bambssquad/boq-tribun-metta/assets/r04/revit/T-01.png

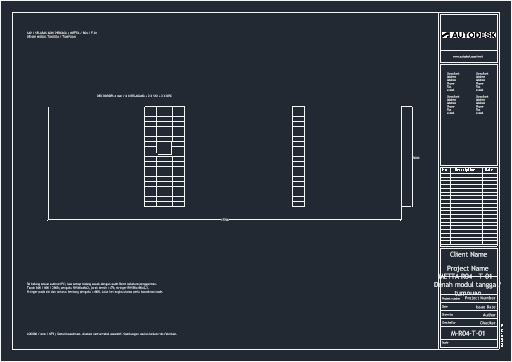
assets/r04/revit/T-01.png
