bambssquad/boq-tribun-metta/assets/r04/revit/T-03.png

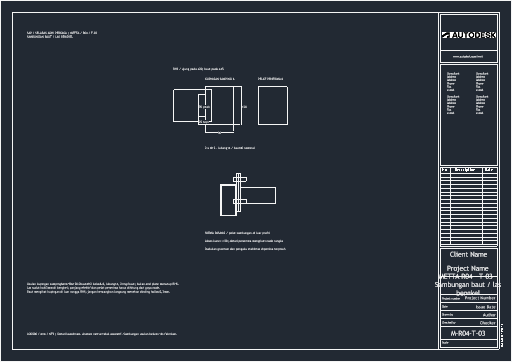
assets/r04/revit/T-03.png
