bambssquad/boq-tribun-metta/assets/r04/revit/T-04.png

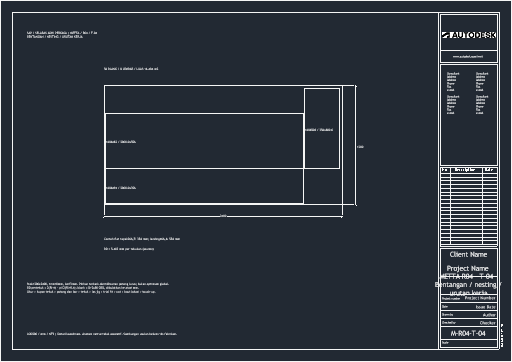
assets/r04/revit/T-04.png
