bambssquad/boq-tribun-metta/assets/technical/revit/S-02.png

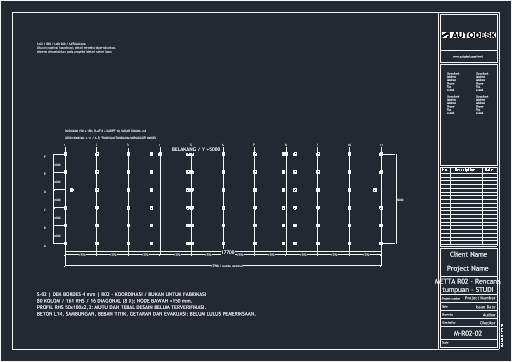
assets/technical/revit/S-02.png
