bambssquad/boq-tribun-metta/assets/technical/revit/S-03.png

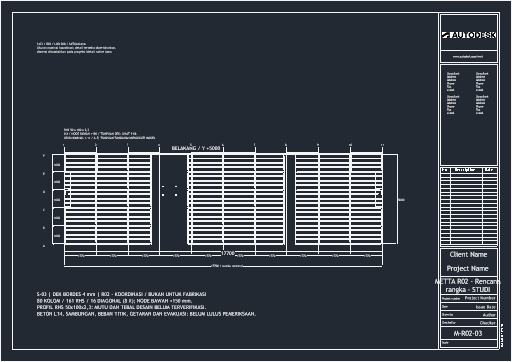
assets/technical/revit/S-03.png
