bambssquad/boq-tribun-metta/assets/technical/revit/S-04.png

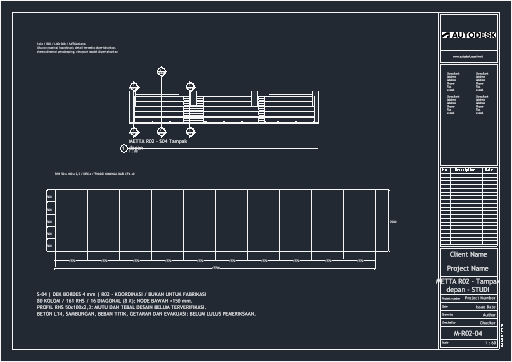
assets/technical/revit/S-04.png
