bambssquad/boq-tribun-metta/assets/technical/revit/S-06.png

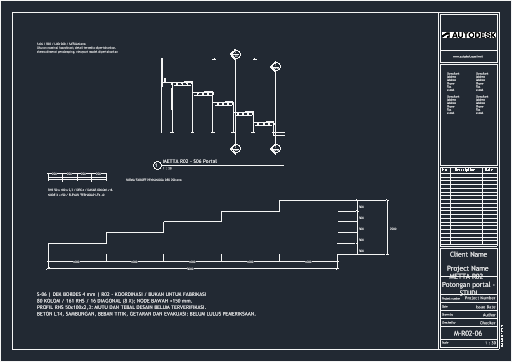
assets/technical/revit/S-06.png
