bambssquad/boq-tribun-metta/assets/technical/revit/S-07.png

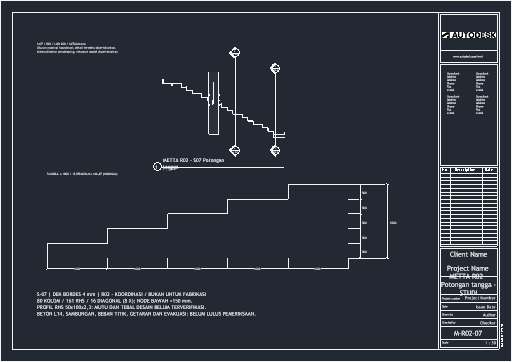
assets/technical/revit/S-07.png
