bambssquad/boq-tribun-metta/assets/technical/revit/S-08.png

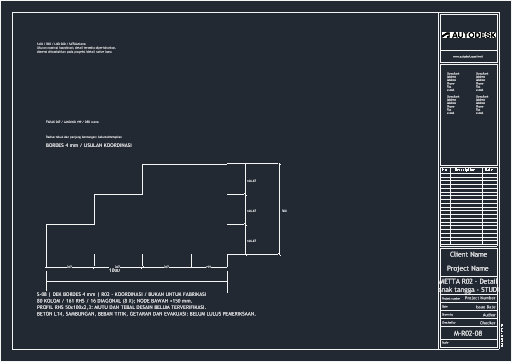
assets/technical/revit/S-08.png
