bambssquad/boq-tribun-metta/assets/technical/revit/S-09.png

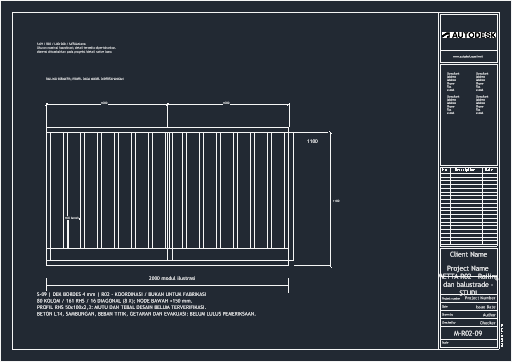
assets/technical/revit/S-09.png
