bambssquad/boq-tribun-metta/assets/technical/revit/S-10.png

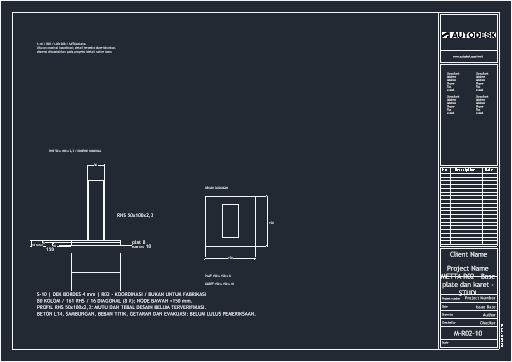
assets/technical/revit/S-10.png
