bambssquad/boq-tribun-metta/assets/technical/revit/S-12.png

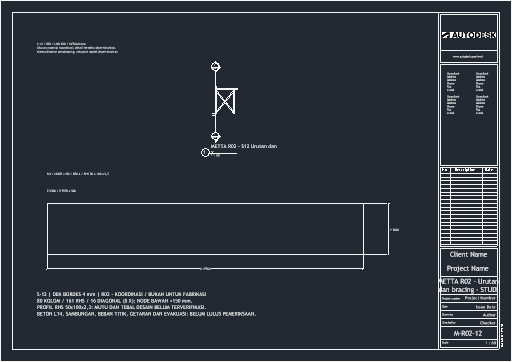
assets/technical/revit/S-12.png
