bambssquad/boq-tribun-metta/assets/technical/S-03.dxf

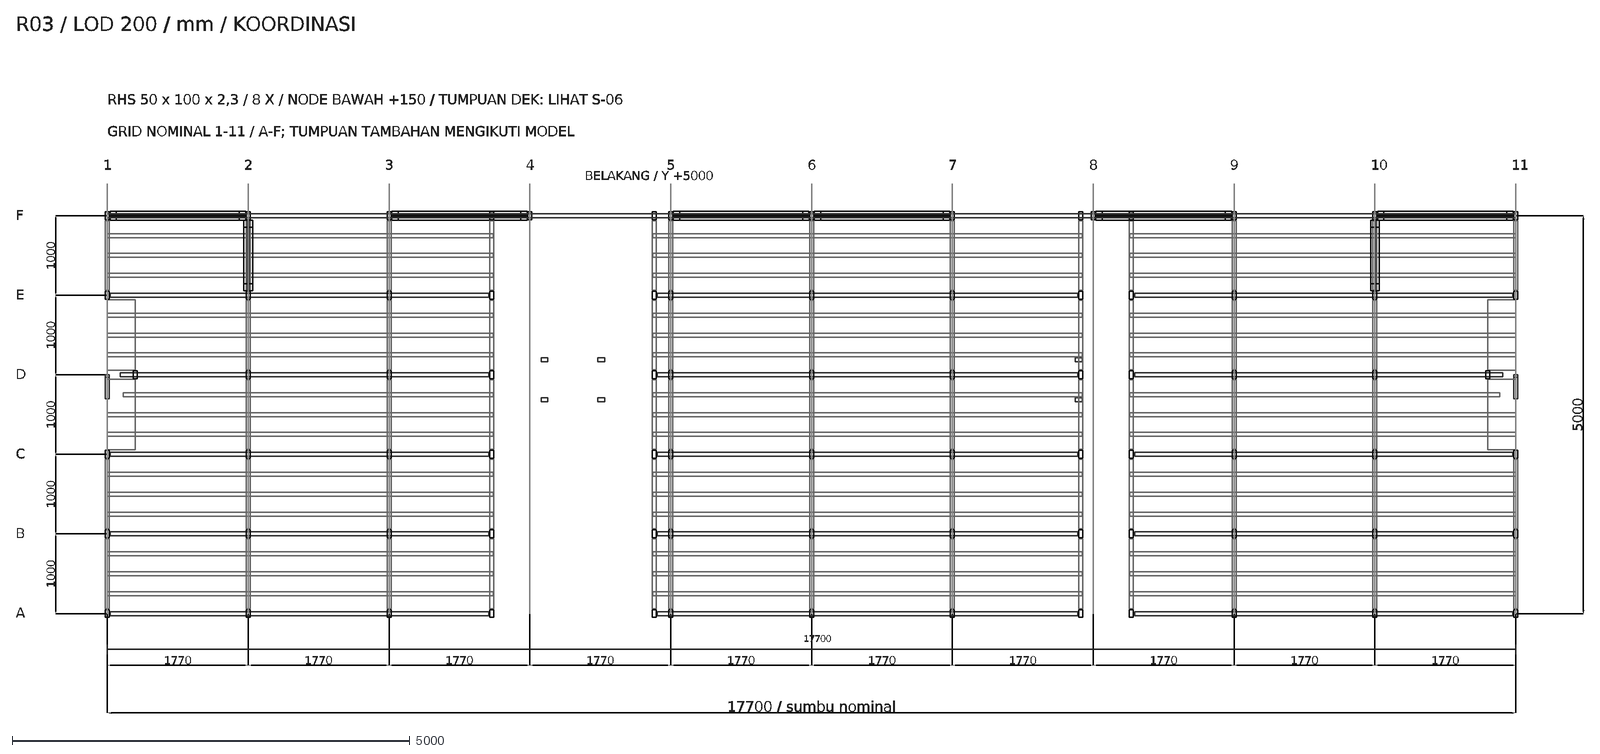
[picture p46: CAD file, 2026-09-08]
assets/technical/S-03.dxf
17700 / sumbu nominal
5000
1770
1000
17700
BELAKANG / Y +5000
1
2
3
4
5
6
7
8
9
10
11
A
B
C
D
E
F
GRID NOMINAL 1-11 / A-F; TUMPUAN TAMBAHAN MENGIKUTI MODEL
RHS 50 x 100 x 2,3 / 8 X / NODE BAWAH +150 / TUMPUAN DEK: LIHAT S-06
R03 / LOD 200 / mm / KOORDINASI
