bambssquad/boq-tribun-metta/assets/technical/S-08.dxf

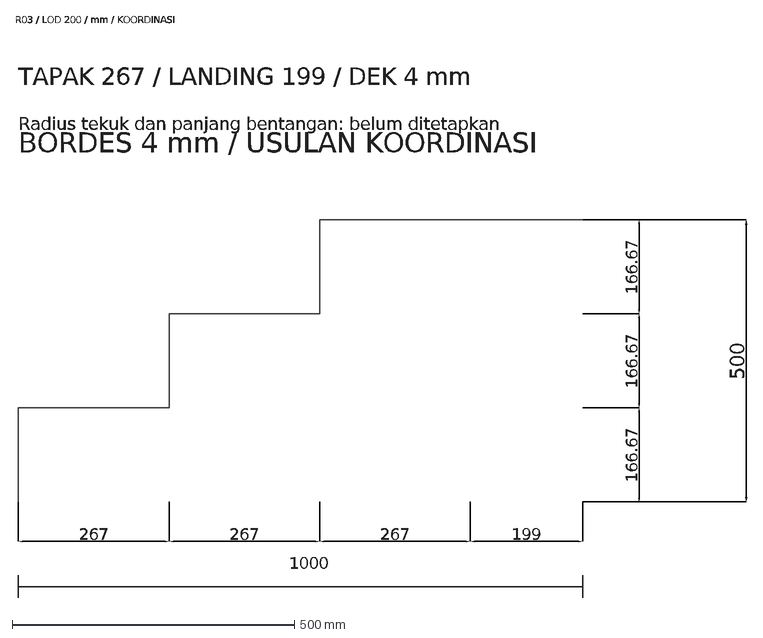
[picture p47: CAD file, 2026-09-08]
assets/technical/S-08.dxf
267
199
166.67
500
1000
BORDES 4 mm / USULAN KOORDINASI
TAPAK 267 / LANDING 199 / DEK 4 mm
Radius tekuk dan panjang bentangan: belum ditetapkan
R03 / LOD 200 / mm / KOORDINASI
