bambssquad/boq-tribun-metta/assets/technical/S-05.dxf

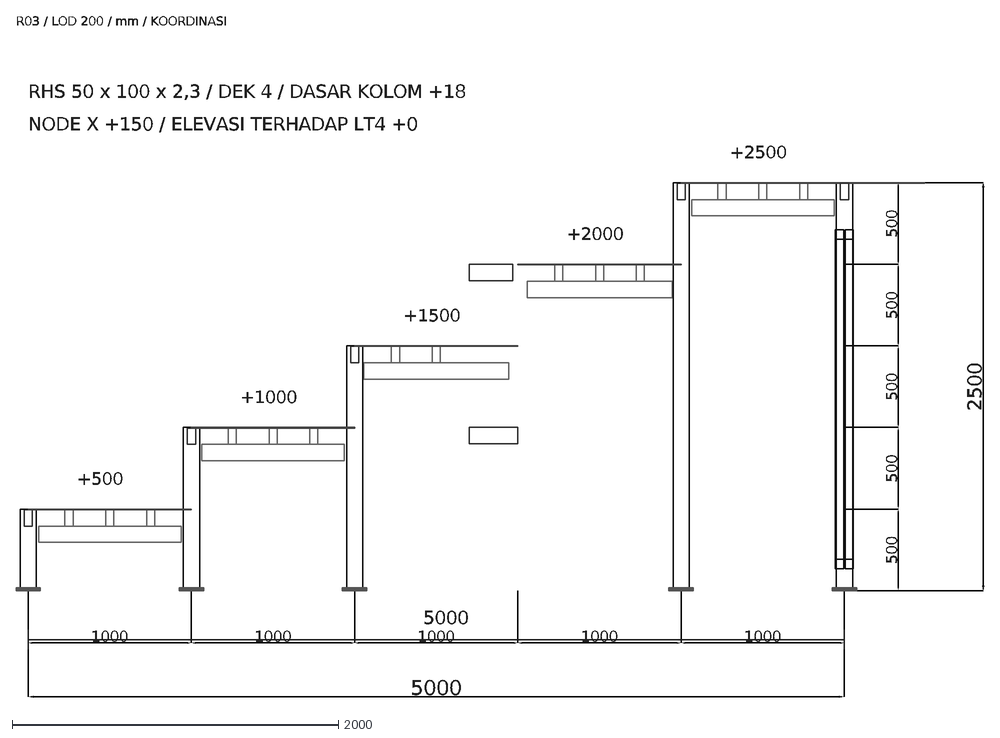
[picture p48: CAD file, 2026-09-08]
assets/technical/S-05.dxf
5000
1000
500
2500
+500
+1000
+1500
+2000
+2500
RHS 50 x 100 x 2,3 / DEK 4 / DASAR KOLOM +18
NODE X +150 / ELEVASI TERHADAP LT4 +0
R03 / LOD 200 / mm / KOORDINASI
